ipTronix/SmartTool/software/ARM/drivers/src/ADC/adc.c

/****************************************************************************
 *   $Id:: adc.c 5901 2010-12-14 19:09:02Z usb00423                         $
 *   Project: NXP LPC11Uxx ADC example
 *
 *   Description:
 *     This file contains ADC code example which include ADC 
 *     initialization, ADC interrupt handler, and APIs for ADC
 *     reading.
*
****************************************************************************
* Software that is described herein is for illustrative purposes only
* which provides customers with programming information regarding the
* products. This software is supplied "AS IS" without any warranties.
* NXP Semiconductors assumes no responsibility or liability for the
* use of the software, conveys no license or title under any patent,
* copyright, or mask work right to the product. NXP Semiconductors
* reserves the right to make changes in the software without
* notification. NXP Semiconductors also make no representation or
* warranty that such application will be suitable for the specified
* use without further testing or modification.

* Permission to use, copy, modify, and distribute this software and its 
* documentation is hereby granted, under NXP Semiconductors' 
* relevant copyright in the software, without fee, provided that it 
* is used in conjunction with NXP Semiconductors microcontrollers.  This 
* copyright, permission, and disclaimer notice must appear in all copies of 
* this code.

****************************************************************************/

#include "LPC11Uxx.h"			/* LPC11xx Peripheral Registers */
#include "ADC/adc.h"
#include "config.h"

#ifndef _BV
#define _BV(_x_) (1UL << (_x_))
#endif

volatile uint32_t ADCValue[ADC_NUM];
volatile uint32_t ADCIntDone = 0;
volatile uint32_t OverRunCounter = 0;

#if BURST_MODE
volatile uint32_t channel_flag = 0; 
#endif

#if ADC_INTERRUPT_FLAG
/******************************************************************************
** Function name:		ADC_IRQHandler
**
** Descriptions:		ADC interrupt handler
**
** parameters:			None
** Returned value:		None
** 
******************************************************************************/
void ADC_IRQHandler (void) 
{
  uint32_t regVal;
  volatile uint32_t dummy;
  int i;
  
  regVal = LPC_ADC->STAT;		/* Read ADC will clear the interrupt */
  if ( regVal & 0x0000FF00 )	/* check OVERRUN error first */
  {
  	OverRunCounter++;
  	for ( i = 0; i < ADC_NUM; i++ )
  	{
  	  regVal = (regVal & 0x0000FF00) >> 0x08;
  	  /* if overrun, just read ADDR to clear */
  	  /* regVal variable has been reused. */
      if ( regVal & _BV(i) )
  	  {
        dummy = LPC_ADC->DR[i];
  	  }
  	}
	LPC_ADC->CR &= ~((0x7<<24)|(0x1<<16));	/* stop ADC now, turn off BURST bit. */ 
  	LPC_ADC->CR &= 0xF8FeFF00;	/* stop ADC now */
  	ADCIntDone = 1;
  	return;	
  }
    
  for ( i = 0; i < ADC_NUM; i++ )
  {
    if ( regVal & _BV(i) )
      ADCValue[i] = ( LPC_ADC->DR[i] >> 6 ) & 0x3FF;
  }

#if BURST_MODE
  channel_flag |= (regVal & 0xFF);
  if ( (channel_flag & 0xFF) == 0x0F )
  {
  	/* All the bits in have been set, it indicates all the ADC 
  	channels have been converted. */
  	LPC_ADC->CR &= 0xF8FeFFFF;	/* stop ADC now */
#if ADGINTEN
    dummy = LPC_ADC->GDR;
#endif
  	channel_flag = 0; 
  	ADCIntDone = 1;
  }
#else
  LPC_ADC->CR &= ~(0x7<<24);	/* stop ADC now */ 
  ADCIntDone = 1;
#endif
  return;
}
#endif

/*****************************************************************************
** Function name:		ADCInit
**
** Descriptions:		initialize ADC channel
**
** parameters:			ADC clock rate
** Returned value:		None
** 
*****************************************************************************/
void ADCInit( uint32_t ADC_Clk )
{
  uint32_t i;

  /* Disable Power down bit to the ADC block. */  
  LPC_SYSCON->PDRUNCFG &= ~(0x1<<4);

  /* Enable AHB clock to the ADC. */
  LPC_SYSCON->SYSAHBCLKCTRL |= (1<<13);

  for ( i = 0; i < ADC_NUM; i++ )
  {
	  ADCValue[i] = 0x0;
  }
  /* Unlike some other pings, for ADC test, all the pins need
  to set to analog mode. Bit 7 needs to be cleared according 
  to design team. */
#if 0
  LPC_IOCON->TDI_PIO0_11 &= ~0x9F; /*  ADC I/O config */
  LPC_IOCON->TDI_PIO0_11 |= 0x02;  /* ADC IN0 */
  LPC_IOCON->TMS_PIO0_12 &= ~0x9F;	
  LPC_IOCON->TMS_PIO0_12 |= 0x02;  /* ADC IN1 */
  LPC_IOCON->TDO_PIO0_13 &= ~0x9F;	
  LPC_IOCON->TDO_PIO0_13 |= 0x02;  /* ADC IN2 */
#endif
  LPC_IOCON->TRST_PIO0_14 &= ~0x9F;	
  LPC_IOCON->TRST_PIO0_14 |= 0x02;  /* ADC IN3 */
#if 0
#ifdef __SWD_DISABLED
  LPC_IOCON->SWDIO_PIO0_15 &= ~0x9F;	
  LPC_IOCON->SWDIO_PIO0_15 |= 0x02;  /* ADC IN4 */
#endif
  LPC_IOCON->PIO0_16   &= ~0x9F; /* Clear bit7, change to analog mode. */	
  LPC_IOCON->PIO0_16   |= 0x01;  /* ADC IN5 */
  LPC_IOCON->PIO0_22   &= ~0x9F; /* Clear bit7, change to analog mode. */	
  LPC_IOCON->PIO0_22   |= 0x01;  /* ADC IN6 */
  LPC_IOCON->PIO0_23   &= ~0x9F; /* Clear bit7, change to analog mode. */	
  LPC_IOCON->PIO0_23   |= 0x01;  /* ADC IN7 */
#endif
  LPC_ADC->CR = ( 0x01 << 0 ) |  /* SEL=1,select channel 0~7 on ADC0 */
	( ( SystemCoreClock / ADC_Clk - 1 ) << 8 ) |  /* CLKDIV = Fpclk / 1000000 - 1 */ 
	( 0 << 16 ) | 		/* BURST = 0, no BURST, software controlled */
	( 0 << 17 ) |  		/* CLKS = 0, 11 clocks/10 bits */
	( 0 << 24 ) |  		/* START = 0 A/D conversion stops */
	( 0 << 27 );		/* EDGE = 0 (CAP/MAT singal falling,trigger A/D conversion) */ 

  /* If POLLING, no need to do the following */
#if ADC_INTERRUPT_FLAG
  NVIC_EnableIRQ(ADC_IRQn);
  LPC_ADC->INTEN = 0xFF;		/* Enable all interrupts */
#if ADGINTEN
  LPC_ADC->INTEN |= 0x100;
#endif
#endif
  return;
}

/*****************************************************************************
** Function name:		ADCRead
**
** Descriptions:		Read ADC channel
**
** parameters:			Channel number
** Returned value:		Value read, if interrupt driven, return channel #
** 
*****************************************************************************/
uint32_t ADCRead( uint8_t channelNum )
{
#if !ADC_INTERRUPT_FLAG
  uint32_t regVal, ADC_Data;
#endif

  /* channel number is 0 through 7 */
  if ( channelNum >= ADC_NUM )
  {
	  channelNum = 0;		/* reset channel number to 0 */
  }
  LPC_ADC->CR &= 0xFFFFFF00;
  LPC_ADC->CR |= (1 << 24) | (1 << channelNum);	
				/* switch channel,start A/D convert */
#if !ADC_INTERRUPT_FLAG
  while ( 1 )			/* wait until end of A/D convert */
  {
  	regVal = *(volatile unsigned long *)(LPC_ADC_BASE 
  			+ ADC_OFFSET + ADC_INDEX * channelNum);
  	/* read result of A/D conversion */
  	if ( regVal & ADC_DONE )
  	{
  	  break;
  	}
  }	
        
  LPC_ADC->CR &= 0xF8FFFFFF;	/* stop ADC now */    
  if ( regVal & ADC_OVERRUN )	/* save data when it's not overrun, otherwise, return zero */
  {
	  return ( 0 );
  }
  ADC_Data = ( regVal >> 6 ) & 0x3FF;
  return ( ADC_Data );	/* return A/D conversion value */
#else
  return ( channelNum );	/* if it's interrupt driven, the ADC reading is 
							done inside the handler. so, return channel number */
#endif
}

/*****************************************************************************
** Function name:		ADC0BurstRead
**
** Descriptions:		Use burst mode to convert multiple channels once.
**
** parameters:			None
** Returned value:		None
** 
*****************************************************************************/
void ADCBurstReadStart( void )
{
  if ( LPC_ADC->CR & (0x7<<24) )
  {
	  LPC_ADC->CR &= ~(0x7<<24);
  }
  /* Read all channels, 0 through 7. Be careful that if the ADCx pins is shared
  with SWD CLK or SWD IO. */
  LPC_ADC->CR |= (0x08);
  LPC_ADC->CR |= (0x1<<16);		/* Set burst mode and start A/D convert */
  return;						/* the ADC reading is done inside the
								handler. */
}

/*********************************************************************************
**                            End Of File
*********************************************************************************/
