ipTronix/SmartTool/software/ARM/drivers/src/SI5351/SI5351.c

/*
 * SI5351.c
 *
 *  Created on: 28 Jun 2013
 *      Author: dario
 */

#include "lpc11Uxx.h"
#include "Si5351.h"
#include "I2C/i2c.h"

#define SI5351_ADDR		0xC0
#define F_VCO	675000000

#define SI5351_WRITE_FIELD(reg, field, val)		Si5351_WriteField(reg, field##_MSK, field##_SH, val)
#define SI5351_READ_FIELD(reg, field)			Si5351_ReadField(reg, field##_MSK, field##_SH)

static const uint8_t m_acRegInit[] =
{
  //0,0x00,
  1,0x00,
  2,0x18,
  //3,0xFF,
  3,0x00,
  //4,0x00,
  //5,0x00,
  //6,0x00,
  //7,0x00,
  //8,0x00,
  9,0xff,
  //10,0x00,
  //11,0x00,
  //12,0x00,
  //13,0x00,
  //14,0x00,
 15,0x00,
 //16,0x8F,
 //17,0x9F,
 16,0x0F,
 17,0x1F,
 18,0x83,
 19,0x80,
 20,0x80,
 21,0x80,
 22,0x80,
 23,0x80,
 24,0x00,
 25,0x00,
 26,0x00,
 27,0x01,
 28,0x00,
 29,0x0B,
 30,0x80,
 31,0x00,
 32,0x00,
 33,0x00,
 34,0x00,
 35,0x00,
 36,0x00,
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
/*
184,0x60,
185,0x60,
186,0x00,
187,0xC0,
188,0x00,
189,0x00,
190,0x00,
191,0x00,
192,0x00,
193,0x00,
194,0x00,
195,0x00,
196,0x00,
197,0x00,
198,0x00,
199,0x00,
200,0x00,
201,0x00,
202,0x00,
203,0x00,
204,0x00,
205,0x00,
206,0x00,
207,0x00,
208,0x00,
209,0x00,
210,0x00,
211,0x00,
212,0x00,
213,0x00,
214,0x00,
215,0x00,
216,0x00,
217,0x00,
218,0x00,
219,0x00,
220,0x00,
221,0x0D,
222,0x00,
223,0x00,
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
*/
};

static uint8_t Si5351_ReadReg(uint8_t cRegAddr)
{
	uint8_t cRegVal;

	I2CRead(SI5351_ADDR,cRegAddr, &cRegVal, 1);

	return cRegVal;
}

static uint8_t Si5351_ReadField(uint8_t cRegAddr, uint8_t cMask, uint8_t cShift)
{
	uint8_t cRegValue = Si5351_ReadReg(cRegAddr);

	return (cRegValue & cMask) >> cShift;
}

uint8_t cRegValue;
static uint8_t Si5351_WriteField(uint8_t cRegAddr, uint8_t cMask, uint8_t cShift, uint8_t cValue)
{
	uint8_t acBuffer[3];

	acBuffer[0] = SI5351_ADDR;
	acBuffer[1] = cRegAddr;

	if (cMask == 0xFF)
	{
		acBuffer[2] = cValue;
	}
	else
	{
		cRegValue = Si5351_ReadReg(cRegAddr);
		cRegValue = (cRegValue & ~cMask) | (cValue << cShift);
		acBuffer[2] = cRegValue;
	}

	return (I2CWrite(acBuffer, 3) == 3)? 1 : 0;
}

// ----------------------------------------------------------------------------
// 										API
// ----------------------------------------------------------------------------
uint8_t debugVar = 0;
void Si5351_Initialize(void)
{
	uint16_t i;

	for (i=0; i<sizeof(m_acRegInit); i+=2)
	{
		if (!Si5351_WriteField(m_acRegInit[i], 0xFF, 0, m_acRegInit[i+1]))
		{
			debugVar = 1;
		}
	}

	cRegValue = Si5351_ReadReg(0);
}

void Si5351_OutputEnable(uint8_t bEnable)
{
	if (bEnable == 0)
	{
		Si5351_WriteField(OUT_EN_CTRL_REG, 0xFF, 0, 0xFF);
		SI5351_WRITE_FIELD(CLK0_CTRL_REG, CLK0_PDN, 1);
		SI5351_WRITE_FIELD(CLK1_CTRL_REG, CLK1_PDN, 1);
	}
	else
	{
		Si5351_WriteField(OUT_EN_CTRL_REG, 0xFF, 0, 0xFC);
		SI5351_WRITE_FIELD(CLK0_CTRL_REG, CLK0_PDN, 0);
		SI5351_WRITE_FIELD(CLK1_CTRL_REG, CLK1_PDN, 0);
	}
}

void Si5351_PLLReset(void)
{
	Si5351_WriteField(PLL_RESET_REG, 0xff, 0, 0xAC);
}

void Si5351_OutputFrequency(uint32_t dwFreqHz)
{
	uint32_t P1;
	uint32_t P2;
	uint32_t P3;
	uint32_t a;
	uint32_t b;
	uint32_t c;
	unsigned long long ddwRem;

	Si5351_OutputEnable(0);

	a = F_VCO/dwFreqHz;
	c = 1048575;	//2^20-1
	ddwRem = F_VCO - a*dwFreqHz;
	b = (uint32_t)((c*ddwRem+dwFreqHz/2)/dwFreqHz);

	P1 = 128*a + 128*b/c - 512;
	P2 = 128*b - c*(128*b/c);
	P3 = c;

	SI5351_WRITE_FIELD(MS0_PAR_44_REG, MS0_P1_17_16, (P1>>16) & 3);
	SI5351_WRITE_FIELD(MS0_PAR_45_REG, MS0_P1_15_8, (P1>>8) & 0xFF);
	SI5351_WRITE_FIELD(MS0_PAR_46_REG, MS0_P1_7_0, P1 & 0xFF);

	SI5351_WRITE_FIELD(MS0_PAR_47_REG, MS0_P2_19_16, (P2>>16) & 0x0F);
	SI5351_WRITE_FIELD(MS0_PAR_48_REG, MS0_P2_15_8, (P2>>8) & 0xFF);
	SI5351_WRITE_FIELD(MS0_PAR_49_REG, MS0_P2_7_0, P2 & 0xFF);

	SI5351_WRITE_FIELD(MS0_PAR_47_REG, MS0_P3_19_16, (P3>>16) & 0x0F);
	SI5351_WRITE_FIELD(MS0_PAR_42_REG, MS0_P3_15_8, (P3>>8) & 0xFF);
	SI5351_WRITE_FIELD(MS0_PAR_43_REG, MS0_P3_7_0, P3 & 0xFF);

	SI5351_WRITE_FIELD(MS1_PAR_52_REG, MS1_P1_17_16, (P1>>16) & 3);
	SI5351_WRITE_FIELD(MS1_PAR_53_REG, MS1_P1_15_8, (P1>>8) & 0xFF);
	SI5351_WRITE_FIELD(MS1_PAR_54_REG, MS1_P1_7_0, P1 & 0xFF);

	SI5351_WRITE_FIELD(MS1_PAR_55_REG, MS1_P2_19_16, (P2>>16) & 0x0F);
	SI5351_WRITE_FIELD(MS1_PAR_56_REG, MS1_P2_15_8, (P2>>8) & 0xFF);
	SI5351_WRITE_FIELD(MS1_PAR_57_REG, MS1_P2_7_0, P2 & 0xFF);

	SI5351_WRITE_FIELD(MS1_PAR_55_REG, MS1_P3_19_16, (P3>>16) & 0x0F);
	SI5351_WRITE_FIELD(MS1_PAR_50_REG, MS1_P3_15_8, (P3>>8) & 0xFF);
	SI5351_WRITE_FIELD(MS1_PAR_51_REG, MS1_P3_7_0, P3 & 0xFF);

	Si5351_OutputEnable(1);
	Si5351_PLLReset();
}
